V1pr/CoverUI/Firmware/CoverUI/YardForce/images/IMG_MOD-Stop_RM-ECOW-V100.jpg

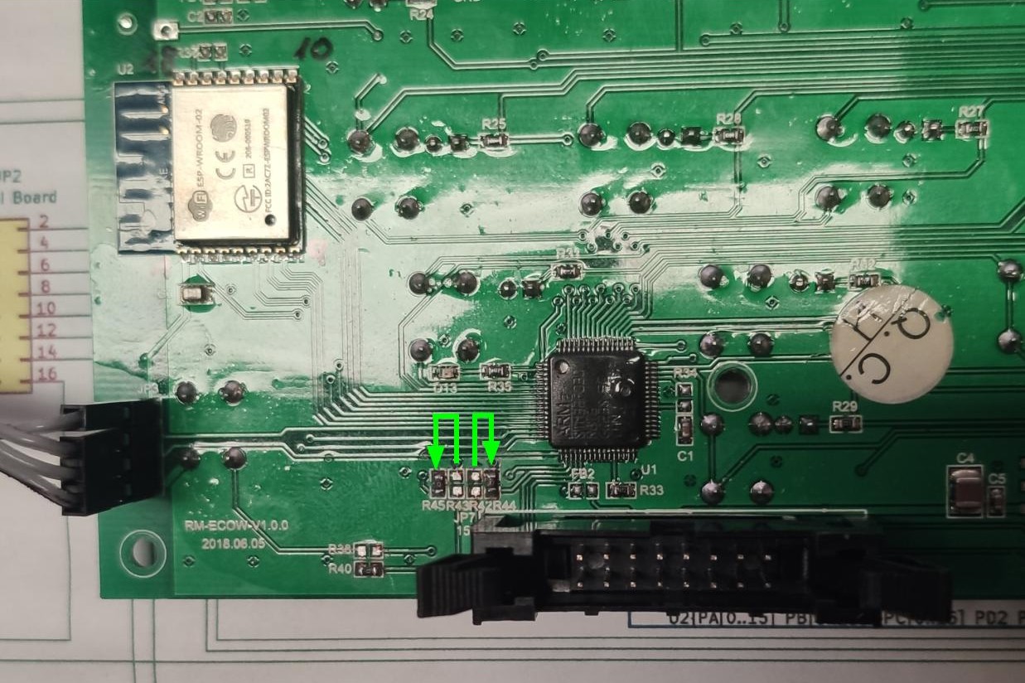
Firmware/CoverUI/YardForce/images/IMG_MOD-Stop_RM-ECOW-V100.jpg
