V1pr/CoverUI/Firmware/CoverUI/YardForce/images/IMG_PCB_Change_Hall-PullUp.jpg

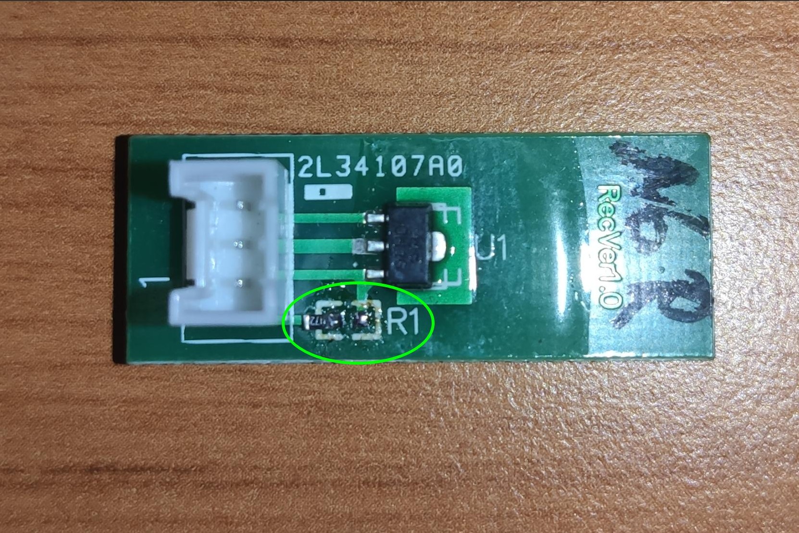
Firmware/CoverUI/YardForce/images/IMG_PCB_Change_Hall-PullUp.jpg
