V1pr/CoverUI/Firmware/CoverUI/YardForce/images/IMG_PCB_Changes_RM-EC3-V11_Stop2.jpg

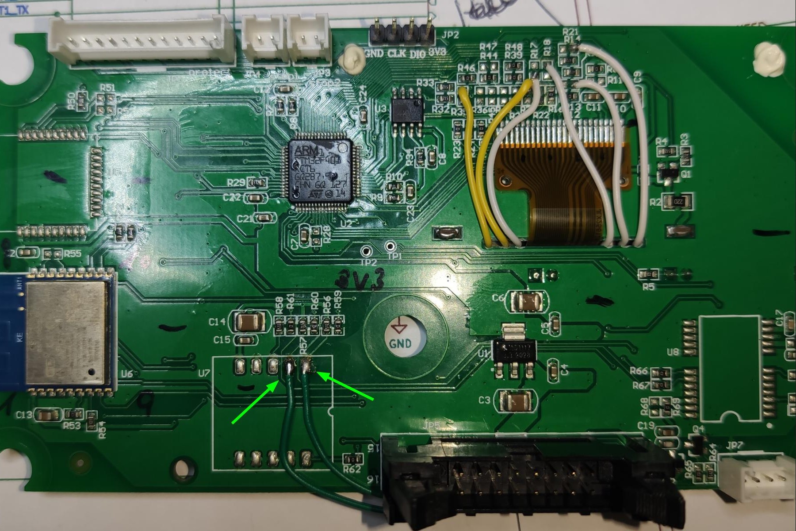
Firmware/CoverUI/YardForce/images/IMG_PCB_Changes_RM-EC3-V11_Stop2.jpg
