V1pr/CoverUI/Firmware/CoverUI/YardForce/images/IMG_PCB_Changes_RM-ECOW-V100.jpg

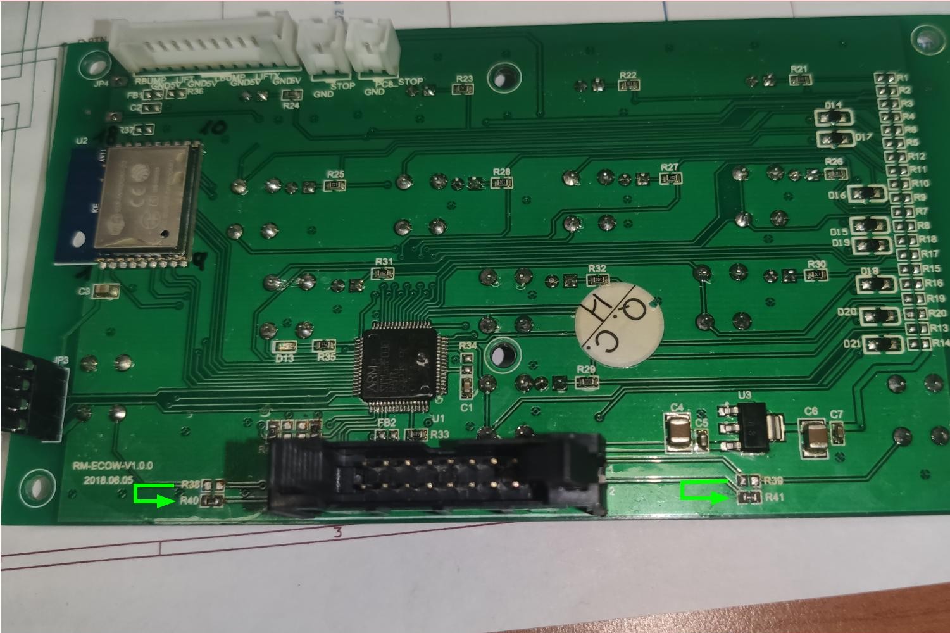
Firmware/CoverUI/YardForce/images/IMG_PCB_Changes_RM-ECOW-V100.jpg
