V1pr/CoverUI/Firmware/CoverUI/YardForce/images/IMG_PCB_Changes_RM-ECOW-V100_Hall2.jpg

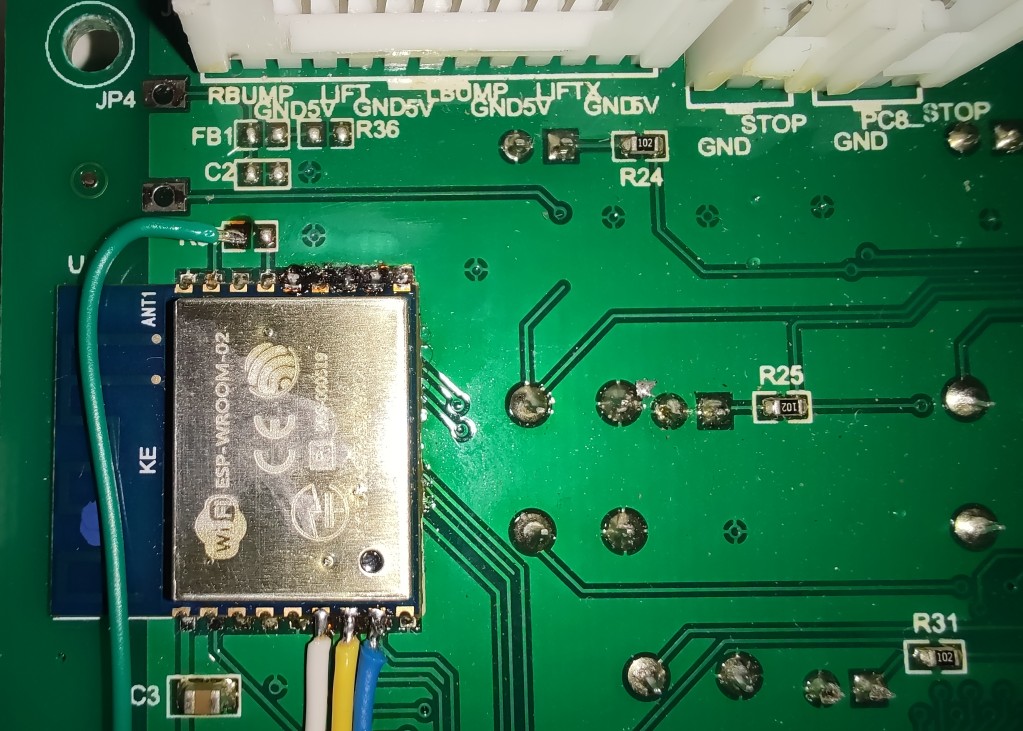
Firmware/CoverUI/YardForce/images/IMG_PCB_Changes_RM-ECOW-V100_Hall2.jpg
