V1pr/CoverUI/Hardware/YardForce/NX100i 18Button-3LED-LCD Board.kicad_sch

## KiCad design Hardware/YardForce/NX100i 18Button-3LED-LCD Board.kicad_sch (2024-08-20)

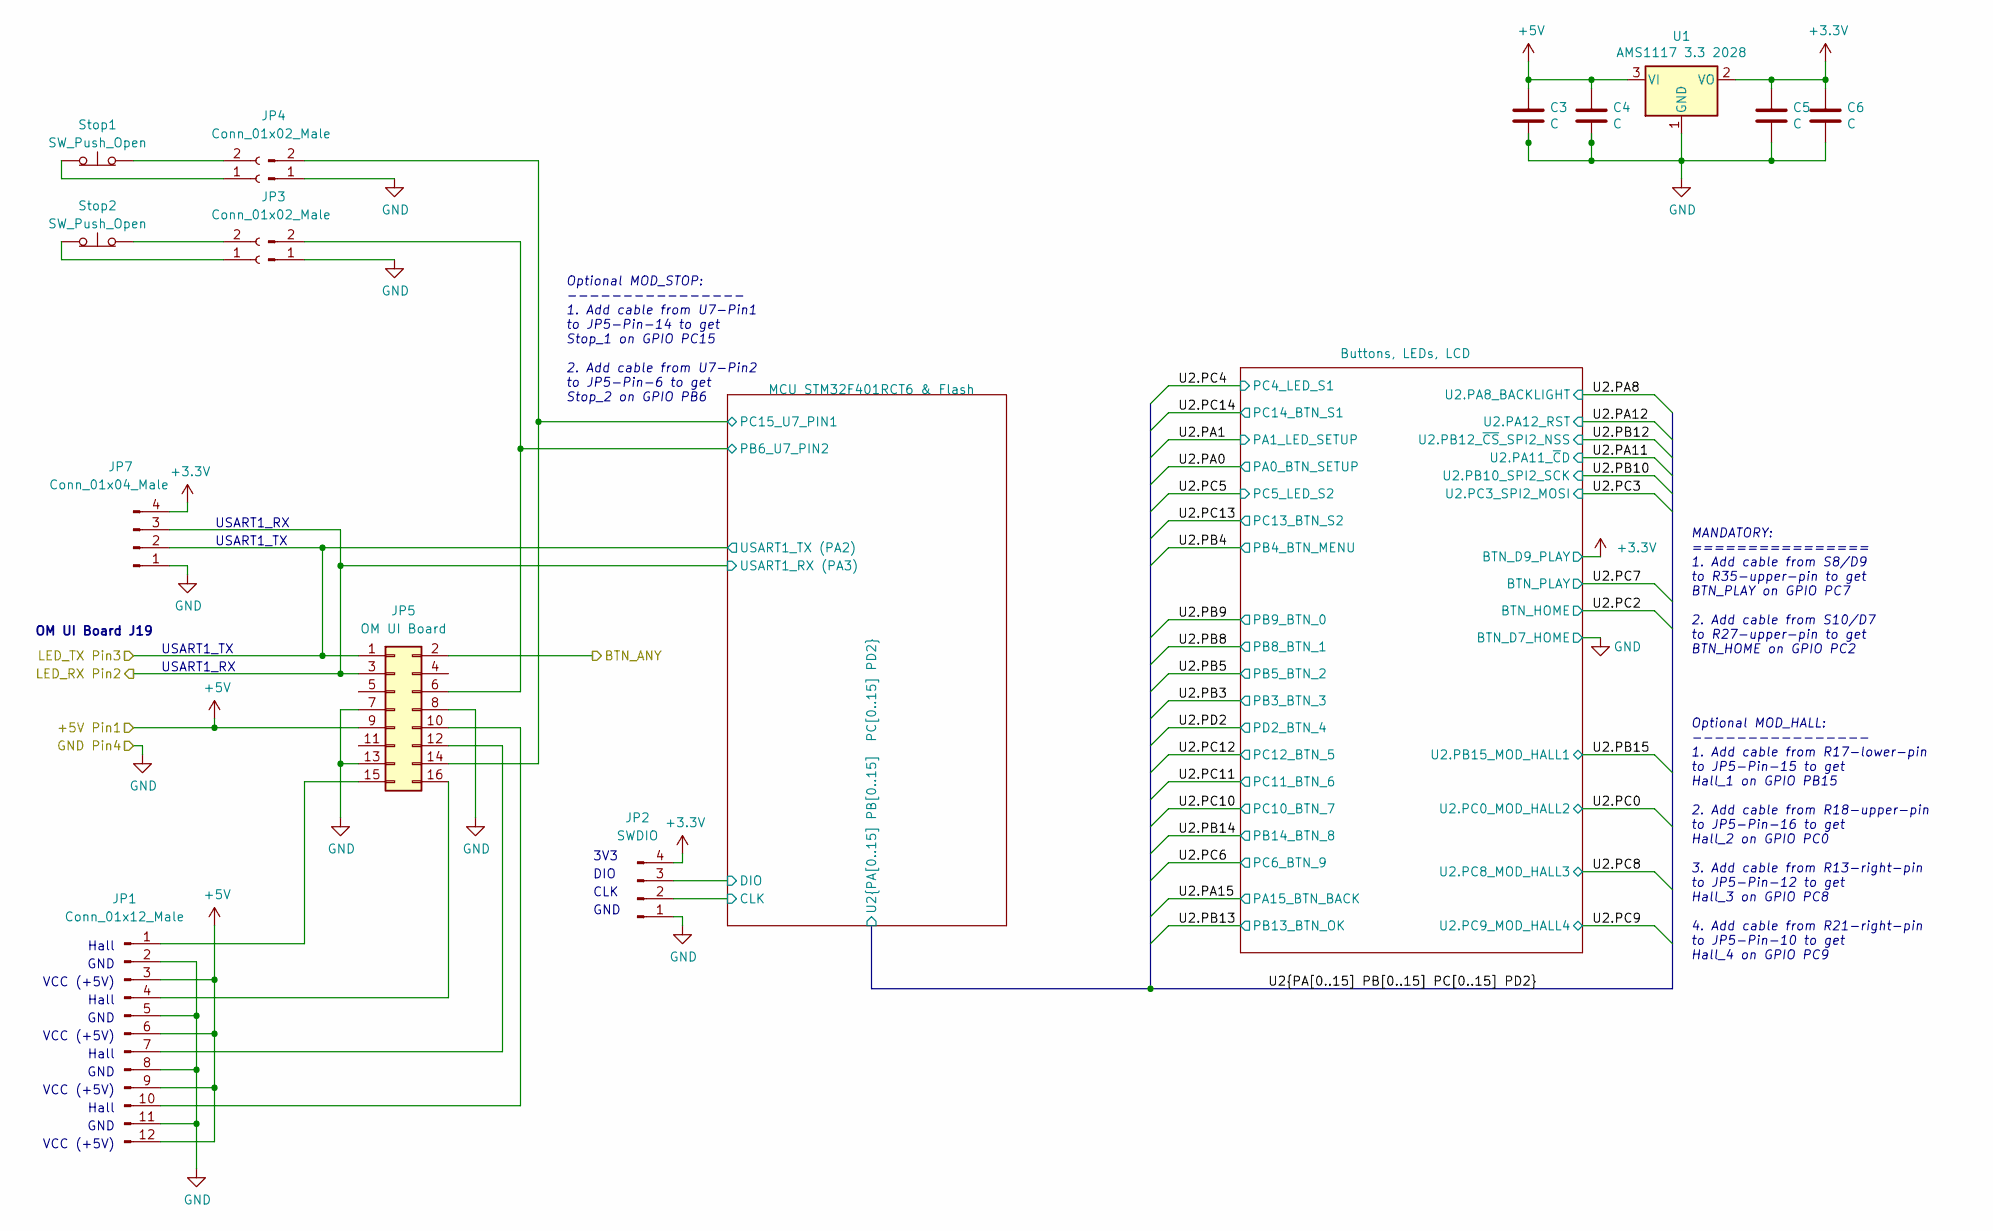
[picture p23: schematic NX100i 18Button-3LED-LCD Board.kicad_sch]

Parts:
C3, C4, C5, C6: C
JP1: Conn_01x12_Male
JP2: SWDIO
JP3, JP4: Conn_01x02_Male
JP5: OM UI Board
JP7: Conn_01x04_Male
Stop1, Stop2: SW_Push_Open
U1: AMS1117 3.3 2028; SOT-223-3_TabPin2

Connections:
+5V Pin1: JP5.9
BTN_ANY: JP5.2
CLK: JP2.2
DIO: JP2.3
LED_RX Pin2: JP5.3, JP7.3
LED_TX Pin3: JP5.1, JP7.2
unnamed: C3.1, C4.1, U1.3 (VI)
unnamed: C3.2, C4.2, C5.2, C6.2, U1.1 (GND)
unnamed: C5.1, C6.1, U1.2 (VO)
unnamed: JP1.1, JP5.15
unnamed: JP1.4, JP5.16
unnamed: JP1.7, JP5.12
unnamed: JP1.10, JP5.10
unnamed: JP1.2, JP1.5, JP1.8, JP1.11
unnamed: JP1.3, JP1.6, JP1.9, JP1.12
unnamed: JP5.7, JP5.13
PB6_U7_PIN2: JP3.2, JP5.6
PC15_U7_PIN1: JP4.2, JP5.14

Notes on the sheet:
DIO
USART1_TX
3V3
VCC (+5V)
GND
Optional MOD_HALL: ---------------- 1. Add cable from R17-lower-pin to JP5-Pin-15 to get Hall_1 on GPIO PB15 2. Add cable from R18-upper-pin to JP5-Pin-16 to get Hall_2 on GPIO PC0 3. Add cable from R13-right-pin to JP5-Pin-12 to get Hall_3 on GPIO PC8 4. Add cable from R21-right-pin to JP5-Pin-10 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
OM UI Board J19
Hall
MANDATORY: ================ 1. Add cable from S8/D9 to R35-upper-pin to get BTN_PLAY on GPIO PC7 2. Add cable from S10/D7 to R27-upper-pin to get BTN_HOME on GPIO PC2
CLK
USART1_RX
Optional MOD_STOP: ---------------- 1. Add cable from U7-Pin1 to JP5-Pin-14 to get Stop_1 on GPIO PC15 2. Add cable from U7-Pin2 to JP5-Pin-6 to get Stop_2 on GPIO PB6
