V1pr/CoverUI/Hardware/YardForce/SA650 9Button-11LED Board.kicad_sch

## KiCad design Hardware/YardForce/SA650 9Button-11LED Board.kicad_sch (2024-08-20)

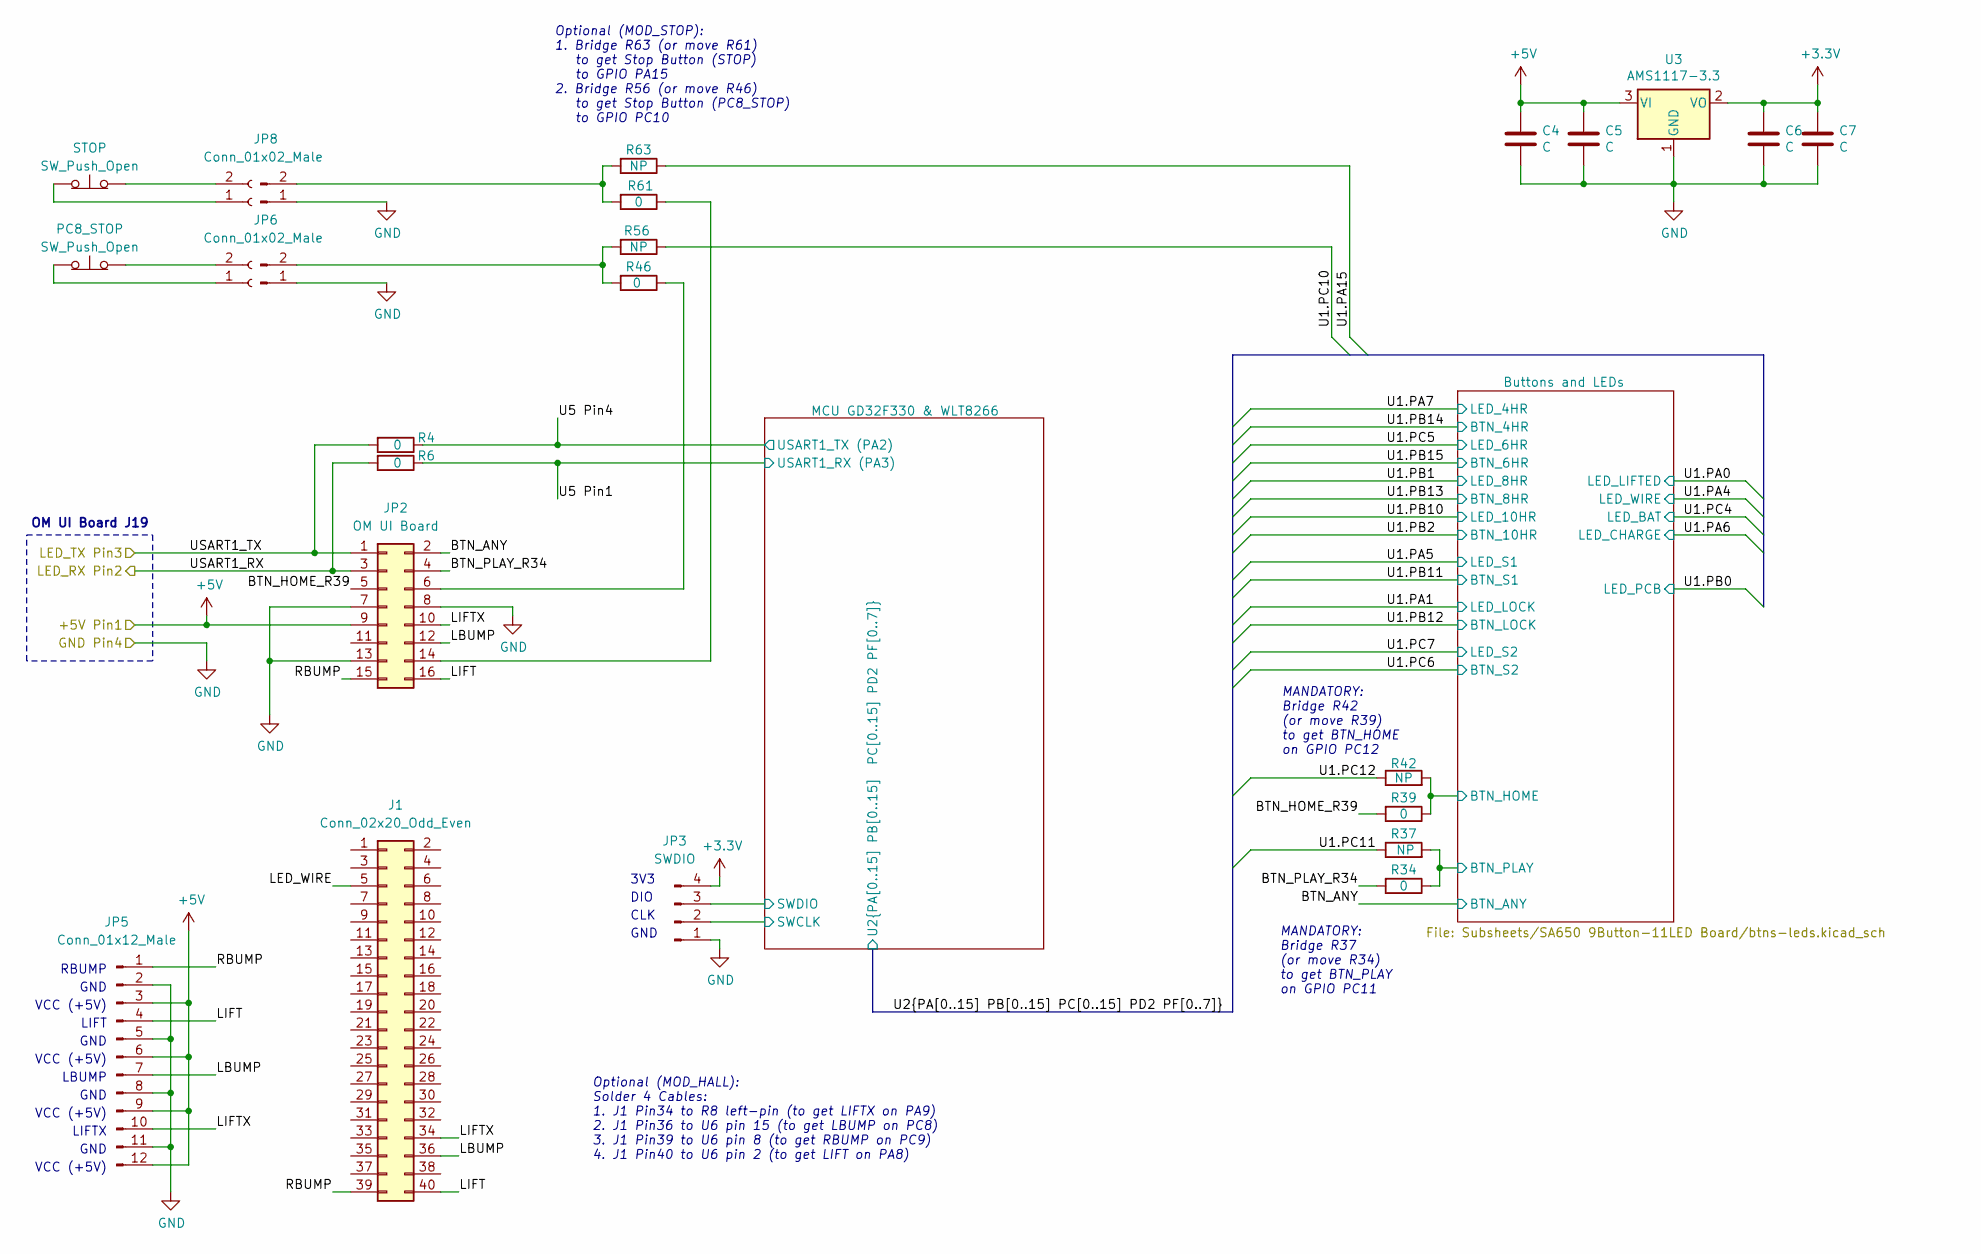
[picture p24: schematic SA650 9Button-11LED Board.kicad_sch]

Parts:
C4, C5, C6, C7: C
J1: Conn_02x20_Odd_Even
JP2: OM UI Board
JP3: SWDIO
JP5: Conn_01x12_Male
JP6, JP8: Conn_01x02_Male
PC8_STOP: SW_Push_Open
R4, R6, R34, R39, R46, R61: 0
R37, R42, R56, R63: NP
STOP: SW_Push_Open
U3: AMS1117-3.3; SOT-223-3_TabPin2

Connections:
+5V Pin1: JP2.9
BTN_ANY: JP2.2
BTN_HOME: R39.1, R42.2
BTN_HOME_R39: JP2.5, R39.2
BTN_PLAY: R34.1, R37.2
BTN_PLAY_R34: JP2.4, R34.2
LBUMP: J1.36, JP2.12, JP5.7
LED_RX Pin2: JP2.3, R6.2
LED_TX Pin3: JP2.1, R4.2
LED_WIRE: J1.5
LIFT: J1.40, JP2.16, JP5.4
LIFTX: J1.34, JP2.10, JP5.10
unnamed: C4.1, C5.1, U3.3 (VI)
unnamed: C4.2, C5.2, C6.2, C7.2, U3.1 (GND)
unnamed: C6.1, C7.1, U3.2 (VO)
unnamed: JP2.6, R46.1
unnamed: JP2.7, JP2.13
unnamed: JP2.14, R61.1
unnamed: JP5.2, JP5.5, JP5.8, JP5.11
unnamed: JP5.3, JP5.6, JP5.9, JP5.12
unnamed: JP6.2, R46.2, R56.2
unnamed: JP8.2, R61.2, R63.2
RBUMP: J1.39, JP2.15, JP5.1
SWCLK: JP3.2
SWDIO: JP3.3
U1.PA15: R63.1
U1.PC10: R56.1
U1.PC11: R37.1
U1.PC12: R42.1
U5 Pin1: R6.1
U5 Pin4: R4.1

Notes on the sheet:
DIO
3V3
VCC (+5V)
GND
OM UI Board J19
RBUMP
CLK
LBUMP
LIFTX
MANDATORY: Bridge R37 (or move R34) to get BTN_PLAY on GPIO PC11
LIFT
MANDATORY: Bridge R42 (or move R39) to get BTN_HOME on GPIO PC12
Optional (MOD_HALL): Solder 4 Cables: 1. J1 Pin34 to R8 left-pin (to get LIFTX on PA9) 2. J1 Pin36 to U6 pin 15 (to get LBUMP on PC8) 3. J1 Pin39 to U6 pin 8 (to get RBUMP on PC9) 4. J1 Pin40 to U6 pin 2 (to get LIFT on PA8)
Optional (MOD_STOP): 1. Bridge R63 (or move R61) to get Stop Button (STOP) to GPIO PA15 2. Bridge R56 (or move R46) to get Stop Button (PC8_STOP) to GPIO PC10
