V1pr/CoverUI/Hardware/YardForce/SA,SC-Type 10Button-12LED Board.kicad_sch

## KiCad design Hardware/YardForce/SA,SC-Type 10Button-12LED Board.kicad_sch (2025-04-15)

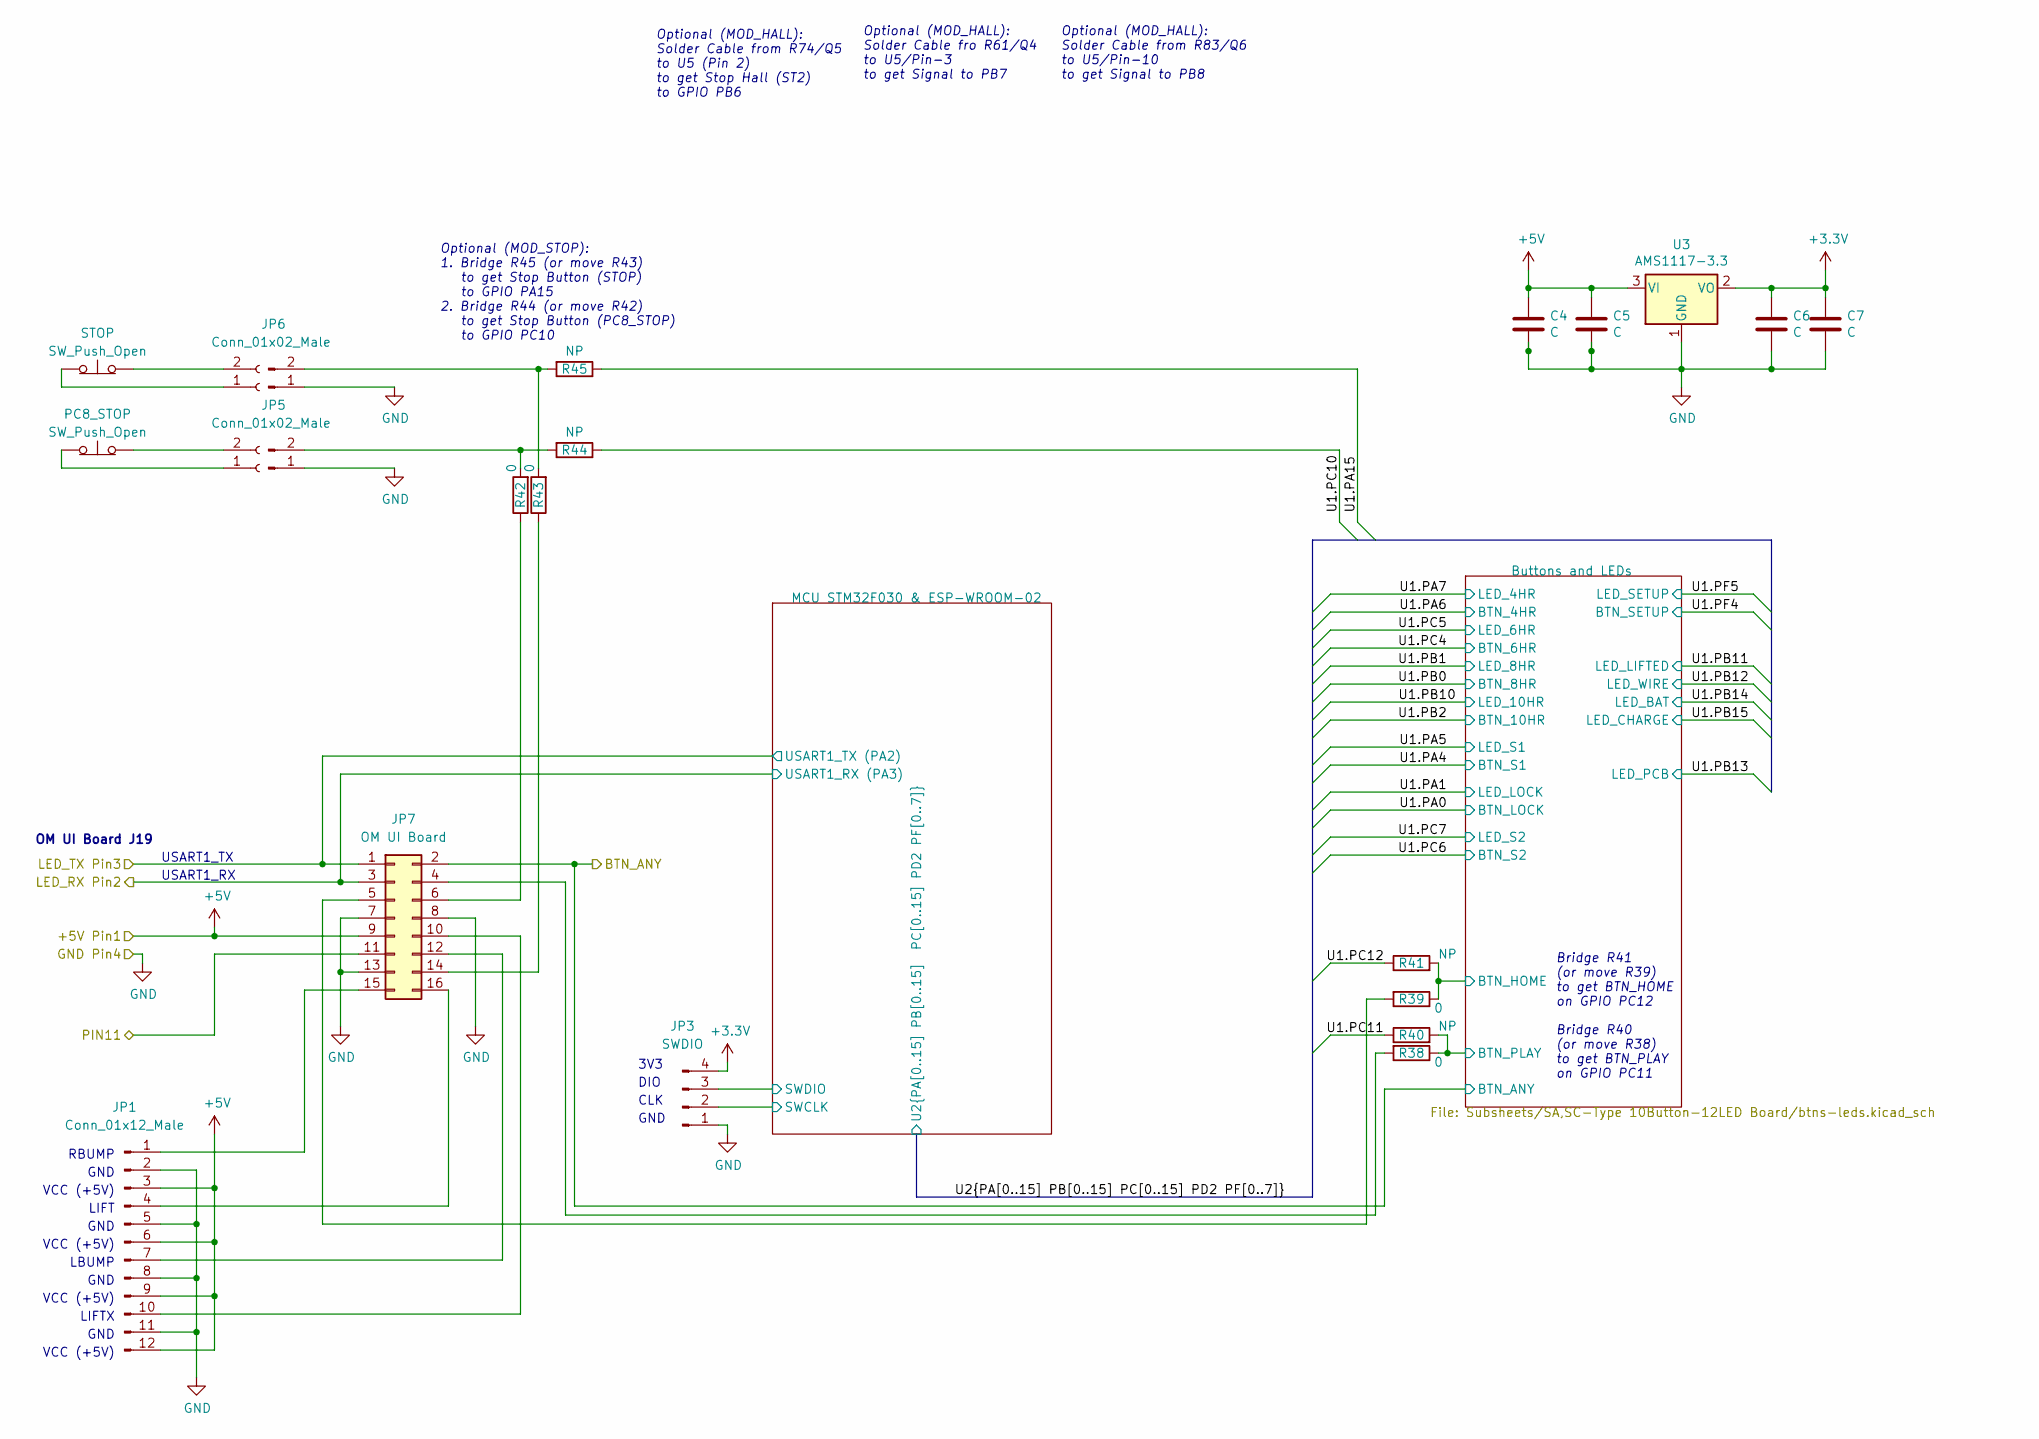
[picture p25: schematic SA,SC-Type 10Button-12LED Board.kicad_sch]

Parts:
C4, C5, C6, C7: C
JP1: Conn_01x12_Male
JP3: SWDIO
JP5, JP6: Conn_01x02_Male
JP7: OM UI Board
PC8_STOP: SW_Push_Open
R38, R39, R42, R43: 0
R40, R41, R44, R45: NP
STOP: SW_Push_Open
U3: AMS1117-3.3; SOT-223-3_TabPin2

Connections:
+5V Pin1: JP7.9
BTN_ANY: JP7.2
BTN_HOME: R39.1, R41.2
BTN_PLAY: R38.1, R40.2
LED_RX Pin2: JP7.3
LED_TX Pin3: JP7.1
unnamed: C4.1, C5.1, U3.3 (VI)
unnamed: C4.2, C5.2, C6.2, C7.2, U3.1 (GND)
unnamed: C6.1, C7.1, U3.2 (VO)
unnamed: JP1.1, JP7.15
unnamed: JP1.4, JP7.16
unnamed: JP1.7, JP7.12
unnamed: JP1.10, JP7.10
unnamed: JP1.2, JP1.5, JP1.8, JP1.11
unnamed: JP1.3, JP1.6, JP1.9, JP1.12
unnamed: JP5.2, R42.2, R44.2
unnamed: JP6.2, R43.2, R45.2
unnamed: JP7.4, R38.2
unnamed: JP7.5, R39.2
unnamed: JP7.6, R42.1
unnamed: JP7.7, JP7.13
unnamed: JP7.14, R43.1
PIN11: JP7.11
SWCLK: JP3.2
SWDIO: JP3.3
U1.PA15: R45.1
U1.PC10: R44.1
U1.PC11: R40.1
U1.PC12: R41.1

Notes on the sheet:
DIO
USART1_TX
3V3
VCC (+5V)
GND
OM UI Board J19
RBUMP
CLK
LBUMP
LIFTX
Bridge R40 (or move R38) to get BTN_PLAY on GPIO PC11
LIFT
Bridge R41 (or move R39) to get BTN_HOME on GPIO PC12
Optional (MOD_HALL): Solder Cable from R74/Q5 to U5 (Pin 2) to get Stop Hall (ST2) to GPIO PB6
Optional (MOD_HALL): Solder Cable from R83/Q6 to U5/Pin-10 to get Signal to PB8
USART1_RX
Optional (MOD_HALL): Solder Cable fro R61/Q4 to U5/Pin-3 to get Signal to PB7
Optional (MOD_STOP): 1. Bridge R45 (or move R43) to get Stop Button (STOP) to GPIO PA15 2. Bridge R44 (or move R42) to get Stop Button (PC8_STOP) to GPIO PC10
