V1pr/CoverUI/Hardware/YardForce/Subsheets/NX100i 18Button-3LED-LCD Board/btn.kicad_sch

## KiCad design Hardware/YardForce/Subsheets/NX100i 18Button-3LED-LCD Board/btn.kicad_sch (2024-08-20)

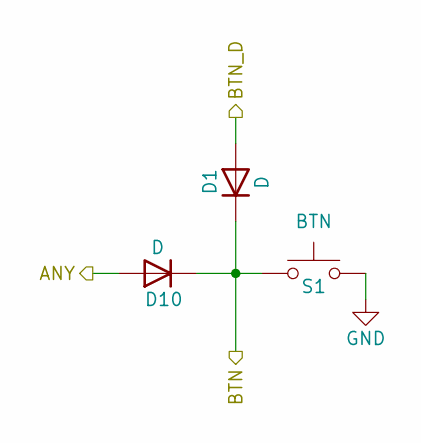
[picture p26: schematic btn.kicad_sch]

Parts:
D1, D10: D
S1: BTN

Connections:
ANY: D10.2 (A)
BTN: D1.1 (K), D10.1 (K), S1.2
BTN_D: D1.2 (A)
