V1pr/CoverUI/Hardware/YardForce/Subsheets/NX100i 18Button-3LED-LCD Board/btns-leds-lcd.kicad_sch

## KiCad design Hardware/YardForce/Subsheets/NX100i 18Button-3LED-LCD Board/btns-leds-lcd.kicad_sch (2024-08-20)

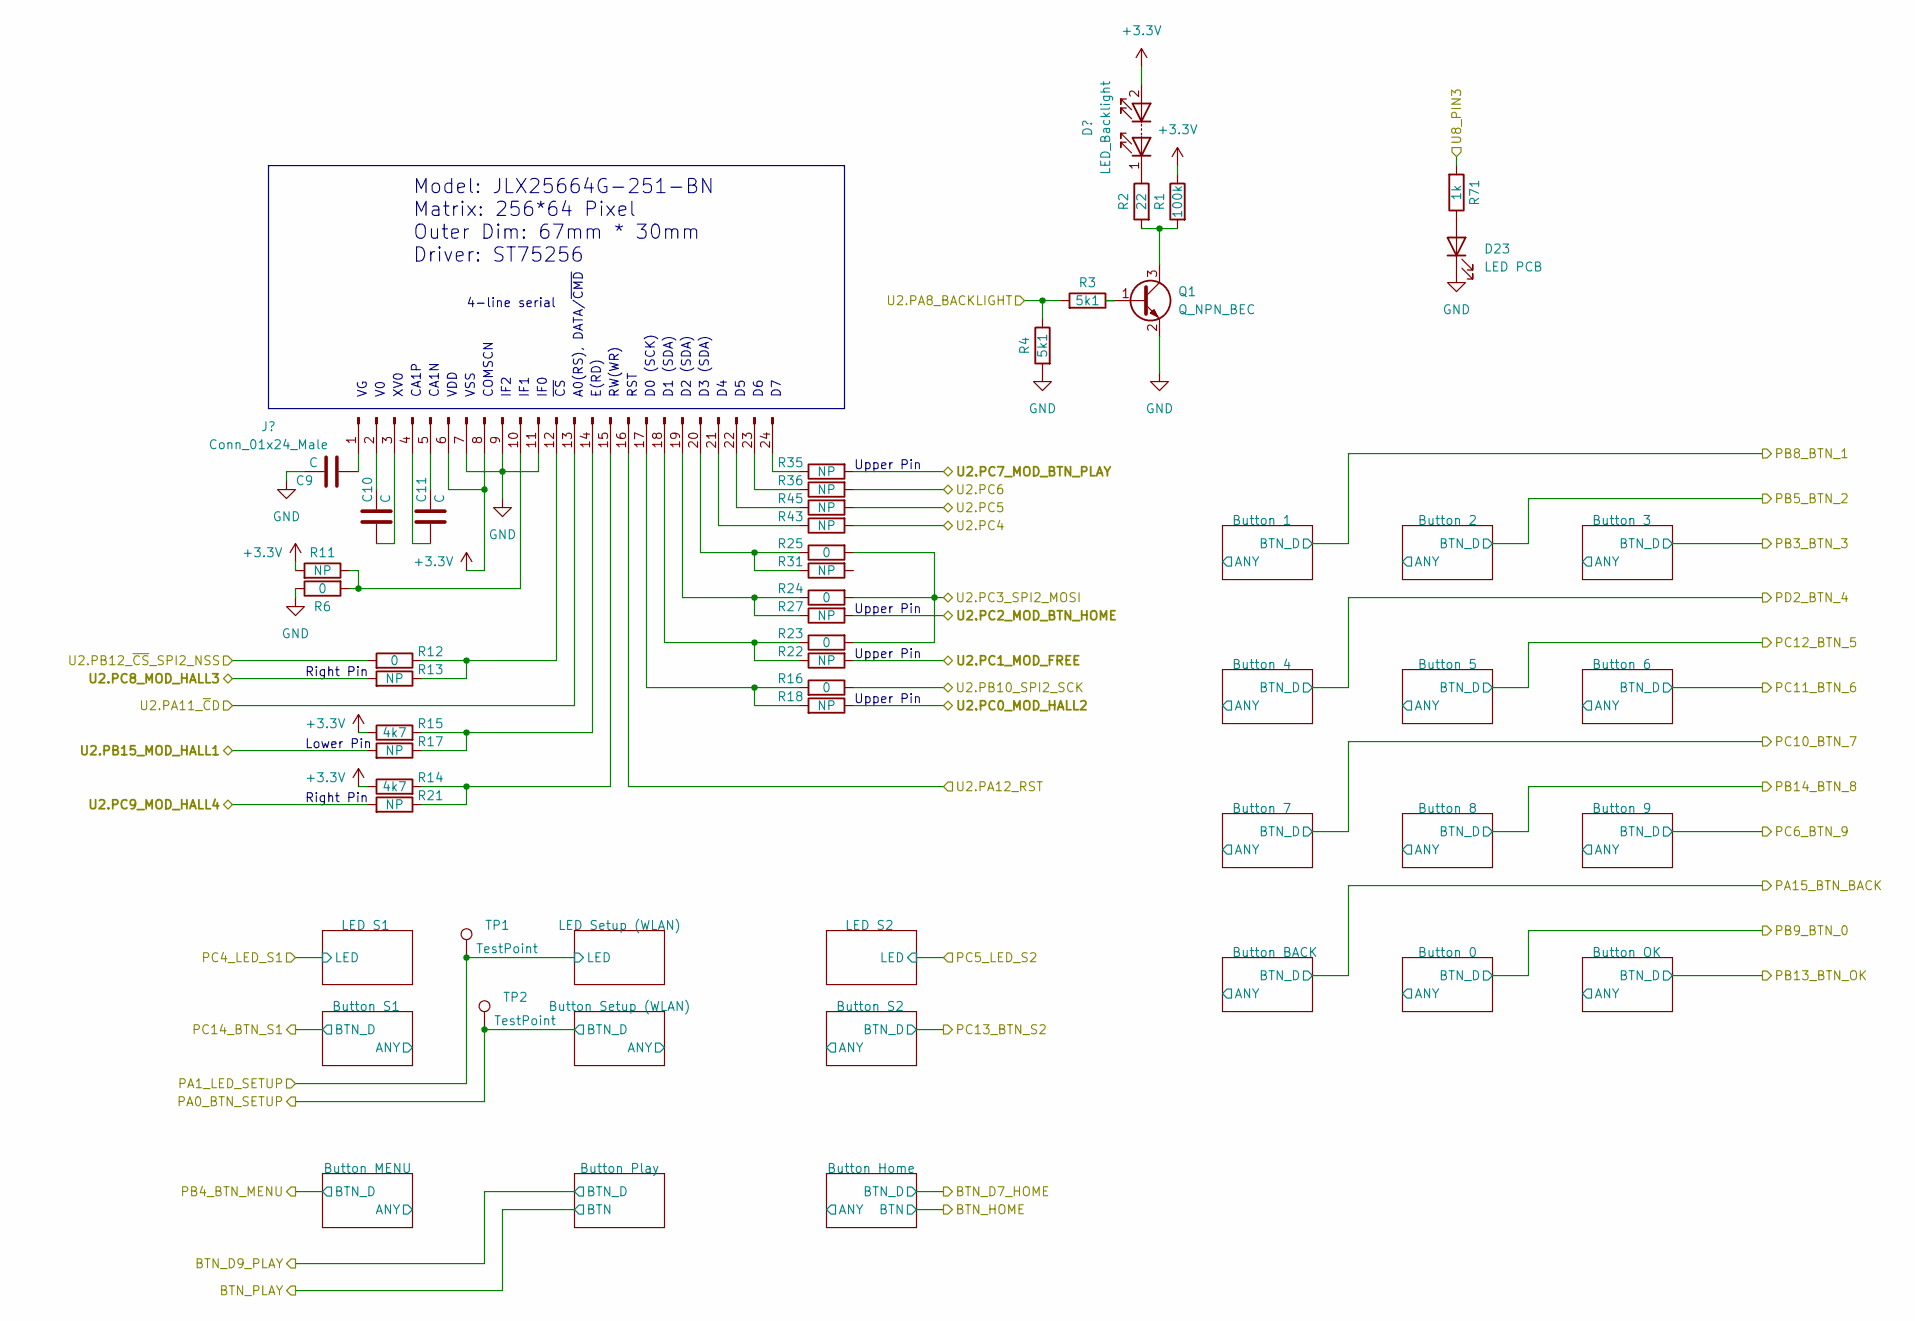
[picture p27: schematic btns-leds-lcd.kicad_sch]

Parts:
C9, C10, C11: C
D23: LED PCB
Q1: Q_NPN_BEC
R1: 100k
R2: 22
R3, R4: 5k1
R6, R12, R16, R23, R24, R25: 0
R11, R13, R17, R18, R21, R22, R27, R31, R35, R36, R43, R45: NP
R14, R15: 4k7
R71: 1k
TP1, TP2: TestPoint

Connections:
unnamed: D23.2 (A), R71.1
unnamed: Q1.1 (B), R3.1
unnamed: Q1.3 (C), R1.2, R2.2
unnamed: R6.2, R11.1
unnamed: R12.1, R13.1
unnamed: R14.2, R21.1
unnamed: R15.2, R17.1
unnamed: R16.2, R18.2
unnamed: R22.1, R23.1
unnamed: R24.1, R27.1
unnamed: R25.1, R31.1
PA0_BTN_SETUP: TP2.1
PA1_LED_SETUP: TP1.1
U2.PA8_BACKLIGHT: R3.2, R4.1
U2.PB10_SPI2_SCK: R16.1
U2.PB12_~CS_SPI2_NSS: R12.2
U2.PB15_MOD_HALL1: R17.2
U2.PC0_MOD_HALL2: R18.1
U2.PC1_MOD_FREE: R22.2
U2.PC2_MOD_BTN_HOME: R27.2
U2.PC3_SPI2_MOSI: R23.2, R24.2, R25.2
U2.PC4: R43.2
U2.PC5: R45.2
U2.PC6: R36.2
U2.PC7_MOD_BTN_PLAY: R35.2
U2.PC8_MOD_HALL3: R13.2
U2.PC9_MOD_HALL4: R21.2
U8_PIN3: R71.2

Notes on the sheet:
RW(WR)
IF2
Right Pin
CA1P
Upper Pin
Model: JLX25664G-251-BN Matrix: 256*64 Pixel Outer Dim: 67mm * 30mm Driver: ST75256
IF0
Lower Pin
CA1N
D1 (SDA)
COMSCN
VSS
D0 (SCK)
D3 (SDA)
E(RD)
~{CS}
XV0
4-line serial
VDD
IF1
D2 (SDA)
RST
A0(RS), DATA/~{CMD}
