V1pr/CoverUI/Hardware/YardForce/Subsheets/NX100i 18Button-3LED-LCD Board/led.kicad_sch

## KiCad design Hardware/YardForce/Subsheets/NX100i 18Button-3LED-LCD Board/led.kicad_sch (2024-08-20)

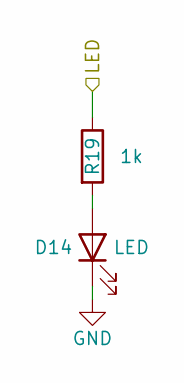
[picture p28: schematic led.kicad_sch]

Parts:
D14: LED
R19: 1k

Connections:
LED: R19.1
unnamed: D14.2 (A), R19.2
