V1pr/CoverUI/Hardware/YardForce/Subsheets/NX100i 18Button-3LED-LCD Board/mcu_stm32f401.kicad_sch

## KiCad design Hardware/YardForce/Subsheets/NX100i 18Button-3LED-LCD Board/mcu_stm32f401.kicad_sch (2024-08-20)

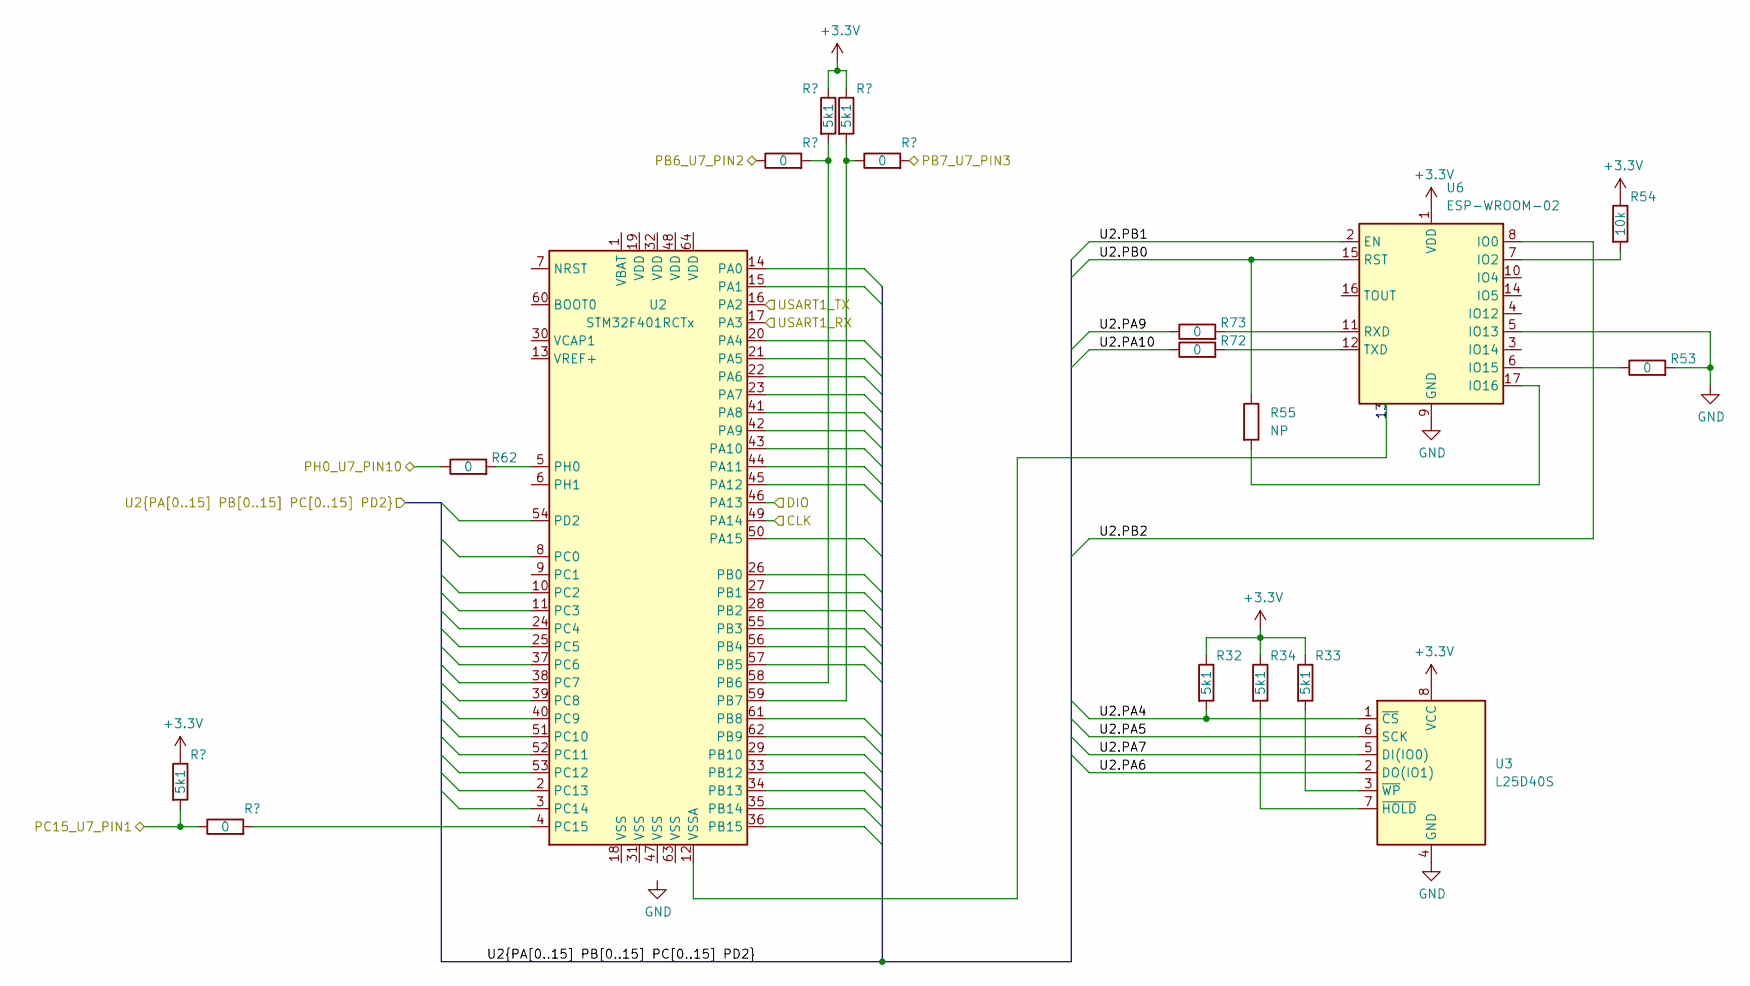
[picture p29: schematic mcu_stm32f401.kicad_sch]

Parts:
R32, R33, R34: 5k1
R53, R62, R72, R73: 0
R54: 10k
R55: NP
U2: STM32F401RCTx; LQFP-64_10x10mm_P0.5mm
U3: L25D40S; SOIC-8_3.9x4.9mm_P1.27mm
U6: ESP-WROOM-02

Connections:
CLK: U2.49 (PA14)
DIO: U2.46 (PA13)
unnamed: R32.1, R33.1, R34.1
unnamed: R33.2, U3.3 (~WP)
unnamed: R34.2, U3.7 (~HOLD)
unnamed: R53.1, U6.6 (IO15)
unnamed: R53.2, U6.5 (IO13)
unnamed: R54.2, U6.7 (IO2)
unnamed: R55.2, U6.17 (IO16)
unnamed: R62.2, U2.5 (PH0)
unnamed: R72.2, U6.12 (TXD)
unnamed: R73.2, U6.11 (RXD)
unnamed: U6.9 (GND), U6.13 (GND), U6.18 (GND), U6.19 (GND)
PH0_U7_PIN10: R62.1
U2.PA4: R32.2, U3.1 (~CS)
U2.PA5: U3.6 (SCK)
U2.PA6: U3.2 (DO(IO1))
U2.PA7: U3.5 (DI(IO0))
U2.PA9: R73.1
U2.PA10: R72.1
U2.PB0: R55.1, U6.15 (RST)
U2.PB1: U6.2 (EN)
U2.PB2: U6.8 (IO0)
USART1_RX: U2.17 (PA3)
USART1_TX: U2.16 (PA2)
