V1pr/CoverUI/Hardware/YardForce/Subsheets/SA650 9Button-11LED Board/led.kicad_sch

## KiCad design Hardware/YardForce/Subsheets/SA650 9Button-11LED Board/led.kicad_sch (2024-08-20)

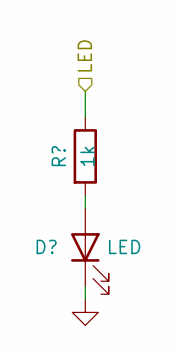
[picture p30: schematic led.kicad_sch]

Parts:
D6: LED
R5: 1k

Connections:
LED: R5.1
unnamed: D6.2 (A), R5.2
