V1pr/CoverUI/Hardware/YardForce/Subsheets/SA650 9Button-11LED Board/mcu_gd32f330.kicad_sch

## KiCad design Hardware/YardForce/Subsheets/SA650 9Button-11LED Board/mcu_gd32f330.kicad_sch (2024-08-20)

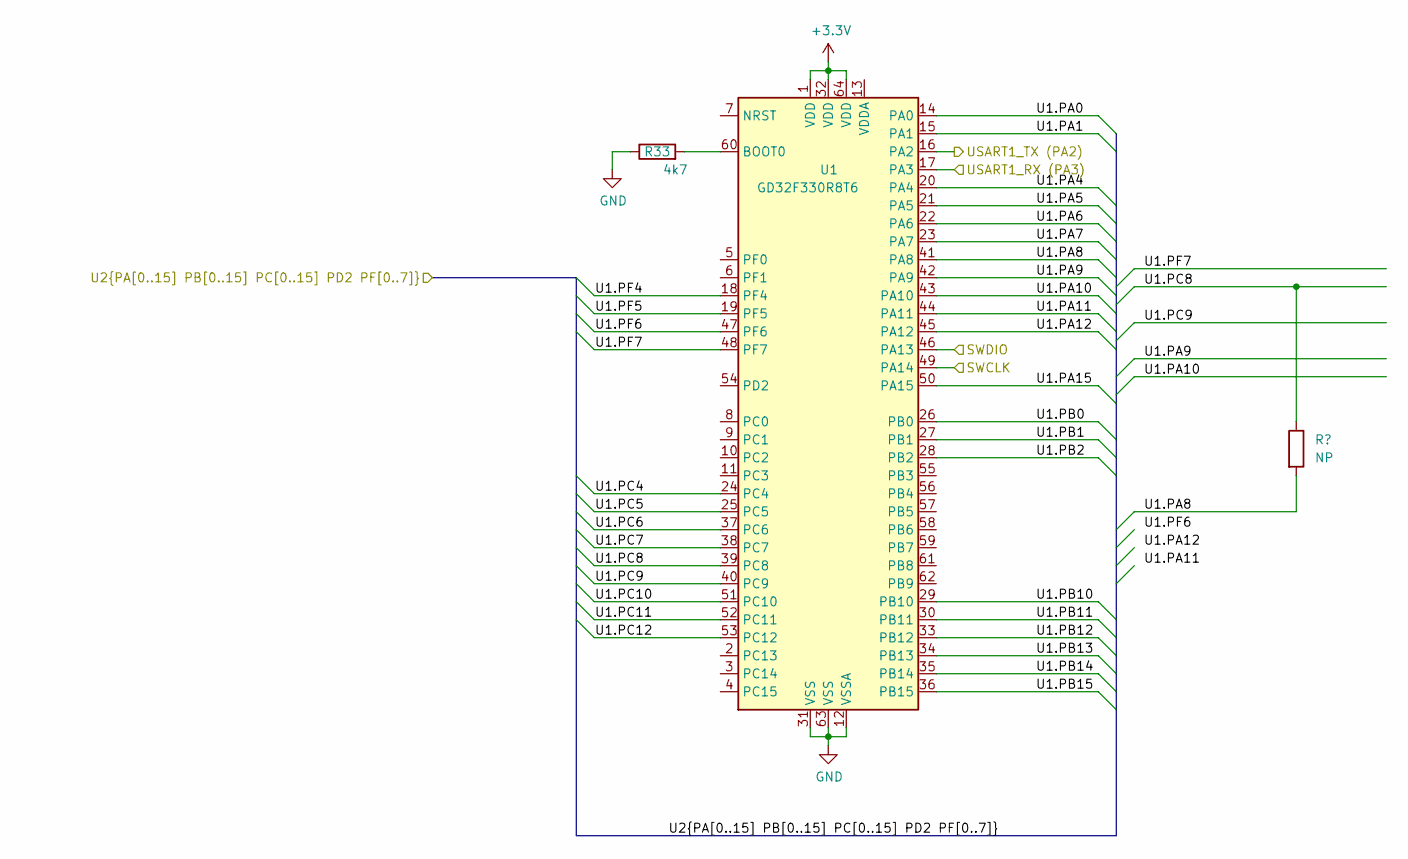
[picture p31: schematic mcu_gd32f330.kicad_sch]

Parts:
R33: 4k7
U1: GD32F330R8T6; LQFP-64_10x10mm_P0.5mm

Connections:
unnamed: R33.2, U1.60 (BOOT0)
unnamed: U1.1 (VDD), U1.32 (VDD), U1.64 (VDD)
unnamed: U1.12 (VSSA), U1.31 (VSS), U1.63 (VSS)
SWCLK: U1.49 (PA14)
SWDIO: U1.46 (PA13)
U1.PA0: U1.14 (PA0)
U1.PA1: U1.15 (PA1)
U1.PA4: U1.20 (PA4)
U1.PA5: U1.21 (PA5)
U1.PA6: U1.22 (PA6)
U1.PA7: U1.23 (PA7)
U1.PA8: U1.41 (PA8)
U1.PA9: U1.42 (PA9)
U1.PA10: U1.43 (PA10)
U1.PA11: U1.44 (PA11)
U1.PA12: U1.45 (PA12)
U1.PA15: U1.50 (PA15)
U1.PB0: U1.26 (PB0)
U1.PB1: U1.27 (PB1)
U1.PB2: U1.28 (PB2)
U1.PB10: U1.29 (PB10)
U1.PB11: U1.30 (PB11)
U1.PB12: U1.33 (PB12)
U1.PB13: U1.34 (PB13)
U1.PB14: U1.35 (PB14)
U1.PB15: U1.36 (PB15)
U1.PC4: U1.24 (PC4)
U1.PC5: U1.25 (PC5)
U1.PC6: U1.37 (PC6)
U1.PC7: U1.38 (PC7)
U1.PC8: U1.39 (PC8)
U1.PC9: U1.40 (PC9)
U1.PC10: U1.51 (PC10)
U1.PC11: U1.52 (PC11)
U1.PC12: U1.53 (PC12)
U1.PF4: U1.18 (PF4)
U1.PF5: U1.19 (PF5)
U1.PF6: U1.47 (PF6)
U1.PF7: U1.48 (PF7)
USART1_RX (PA3): U1.17 (PA3)
USART1_TX (PA2): U1.16 (PA2)
