V1pr/CoverUI/Hardware/YardForce/Subsheets/SA,SC-Type 10Button-12LED Board/led.kicad_sch

## KiCad design Hardware/YardForce/Subsheets/SA,SC-Type 10Button-12LED Board/led.kicad_sch (2025-04-15)

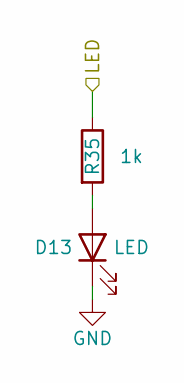
[picture p32: schematic led.kicad_sch]

Parts:
D13: LED
R35: 1k

Connections:
LED: R35.1
unnamed: D13.2 (A), R35.2
