V1pr/CoverUI/Hardware/YardForce/Subsheets/SA,SC-Type 10Button-12LED Board/mcu_stm32f030.kicad_sch

## KiCad design Hardware/YardForce/Subsheets/SA,SC-Type 10Button-12LED Board/mcu_stm32f030.kicad_sch (2025-04-15)

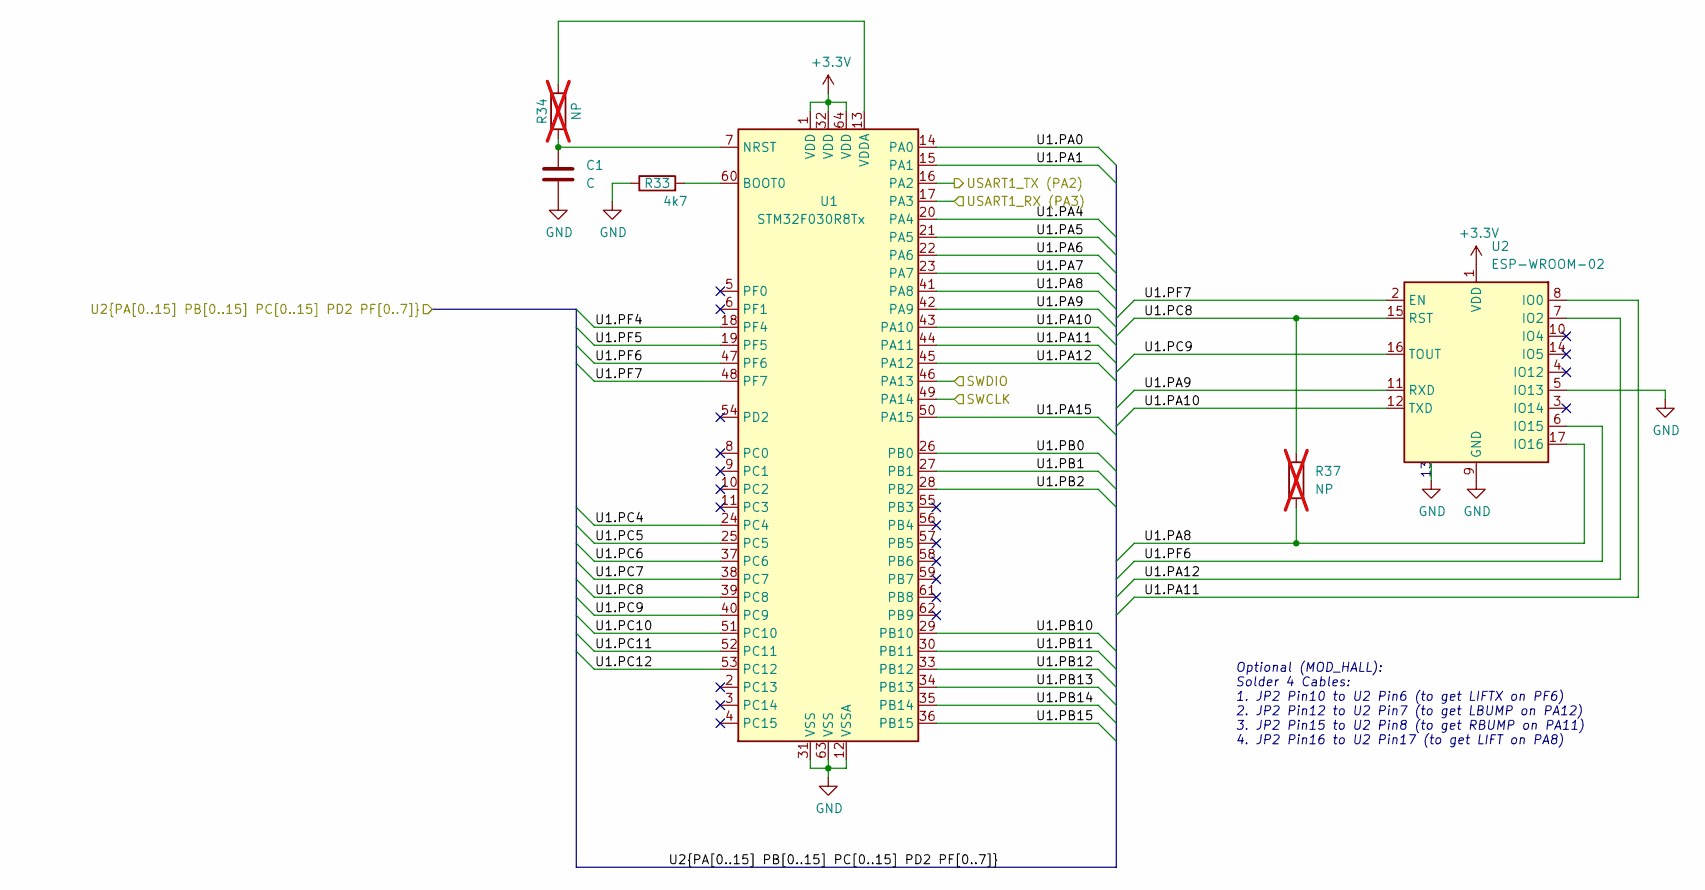
[picture p33: schematic mcu_stm32f030.kicad_sch]

Parts:
C1: C
R33: 4k7
R34, R37: NP; not fitted
U1: STM32F030R8Tx; LQFP-64_10x10mm_P0.5mm
U2: ESP-WROOM-02

Connections:
GND: C1.2, U2.5 (IO13)
unnamed: C1.1, R34.1, U1.7 (NRST)
unnamed: R33.2, U1.60 (BOOT0)
unnamed: R34.2, U1.13 (VDDA)
unnamed: U1.1 (VDD), U1.32 (VDD), U1.64 (VDD)
unnamed: U1.12 (VSSA), U1.31 (VSS), U1.63 (VSS)
unnamed: U2.9 (GND), U2.13 (GND), U2.18 (GND), U2.19 (GND)
SWCLK: U1.49 (PA14)
SWDIO: U1.46 (PA13)
U1.PA0: U1.14 (PA0)
U1.PA1: U1.15 (PA1)
U1.PA4: U1.20 (PA4)
U1.PA5: U1.21 (PA5)
U1.PA6: U1.22 (PA6)
U1.PA7: U1.23 (PA7)
U1.PA8: R37.2, U1.41 (PA8), U2.17 (IO16)
U1.PA9: U1.42 (PA9), U2.11 (RXD)
U1.PA10: U1.43 (PA10), U2.12 (TXD)
U1.PA11: U1.44 (PA11), U2.8 (IO0)
U1.PA12: U1.45 (PA12), U2.7 (IO2)
U1.PA15: U1.50 (PA15)
U1.PB0: U1.26 (PB0)
U1.PB1: U1.27 (PB1)
U1.PB2: U1.28 (PB2)
U1.PB10: U1.29 (PB10)
U1.PB11: U1.30 (PB11)
U1.PB12: U1.33 (PB12)
U1.PB13: U1.34 (PB13)
U1.PB14: U1.35 (PB14)
U1.PB15: U1.36 (PB15)
U1.PC4: U1.24 (PC4)
U1.PC5: U1.25 (PC5)
U1.PC6: U1.37 (PC6)
U1.PC7: U1.38 (PC7)
U1.PC8: R37.1, U1.39 (PC8), U2.15 (RST)
U1.PC9: U1.40 (PC9), U2.16 (TOUT)
U1.PC10: U1.51 (PC10)
U1.PC11: U1.52 (PC11)
U1.PC12: U1.53 (PC12)
U1.PF4: U1.18 (PF4)
U1.PF5: U1.19 (PF5)
U1.PF6: U1.47 (PF6), U2.6 (IO15)
U1.PF7: U1.48 (PF7), U2.2 (EN)
USART1_RX (PA3): U1.17 (PA3)
USART1_TX (PA2): U1.16 (PA2)

Notes on the sheet:
Optional (MOD_HALL): Solder 4 Cables: 1. JP2 Pin10 to U2 Pin6 (to get LIFTX on PF6) 2. JP2 Pin12 to U2 Pin7 (to get LBUMP on PA12) 3. JP2 Pin15 to U2 Pin8 (to get RBUMP on PA11) 4. JP2 Pin16 to U2 Pin17 (to get LIFT on PA8)
